masterchekla/ATX-PSU/docs/images/IMG_4238.jpg

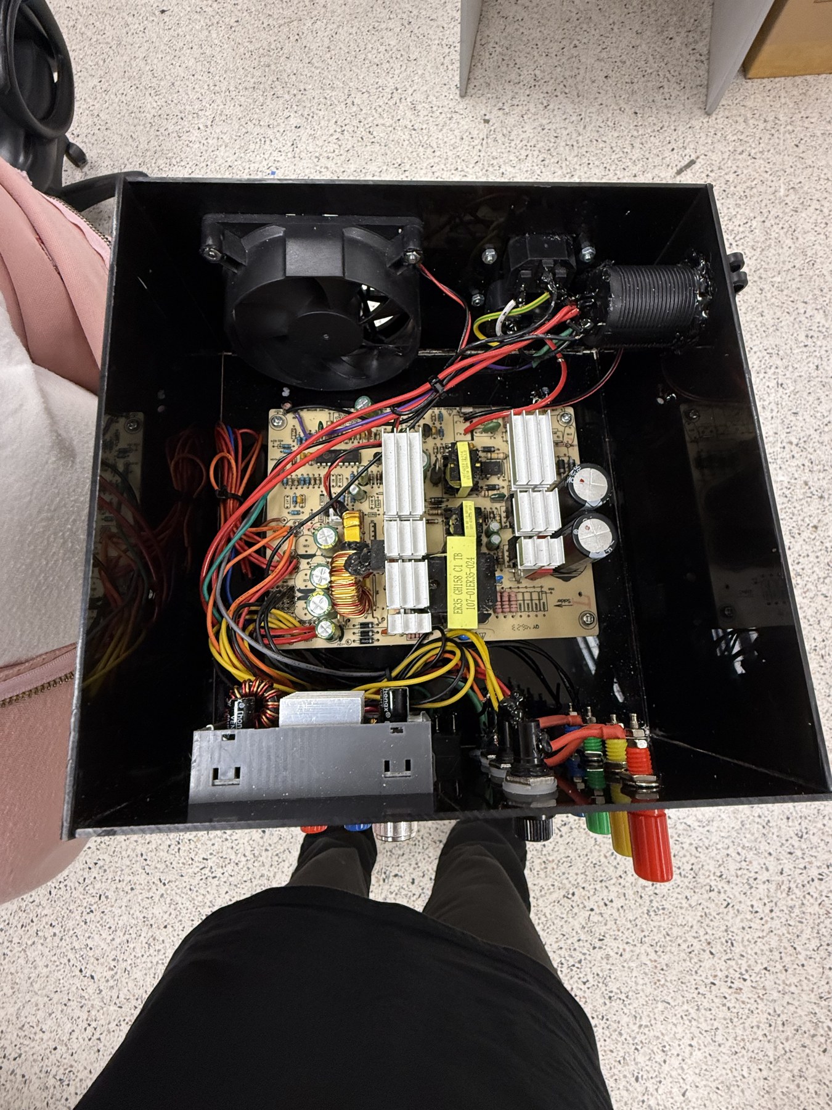
docs/images/IMG_4238.jpg
