masterchekla/ATX-PSU/docs/images/IMG_4239.jpg

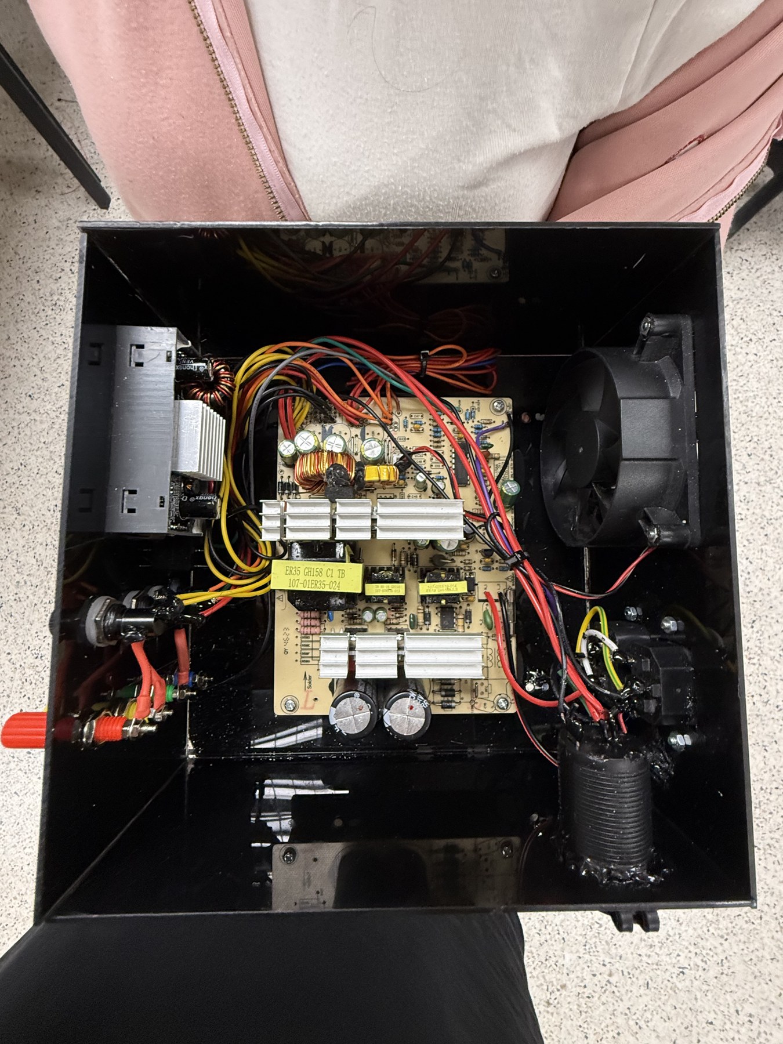
docs/images/IMG_4239.jpg
