masterchekla/ATX-PSU/docs/images/IMG_4240.jpg

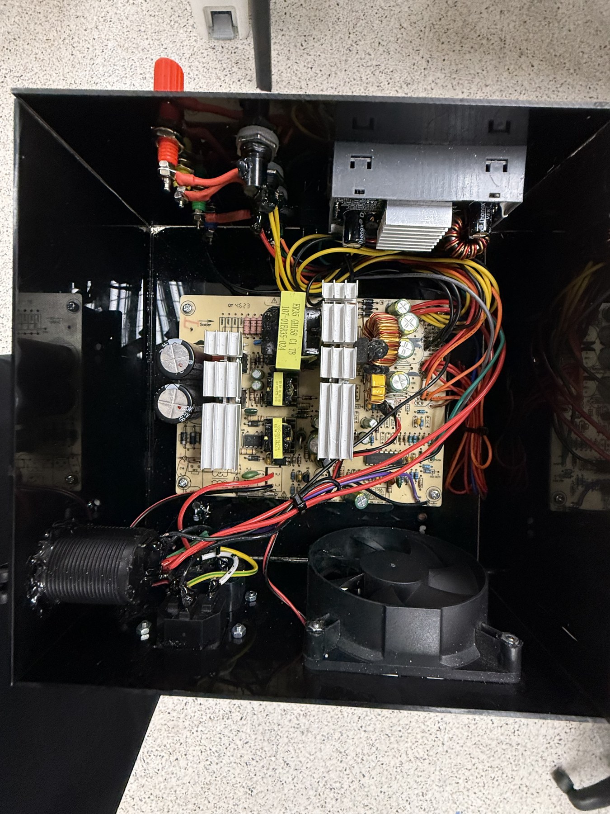
docs/images/IMG_4240.jpg
