masterchekla/ATX-PSU/docs/images/IMG_4241.jpg

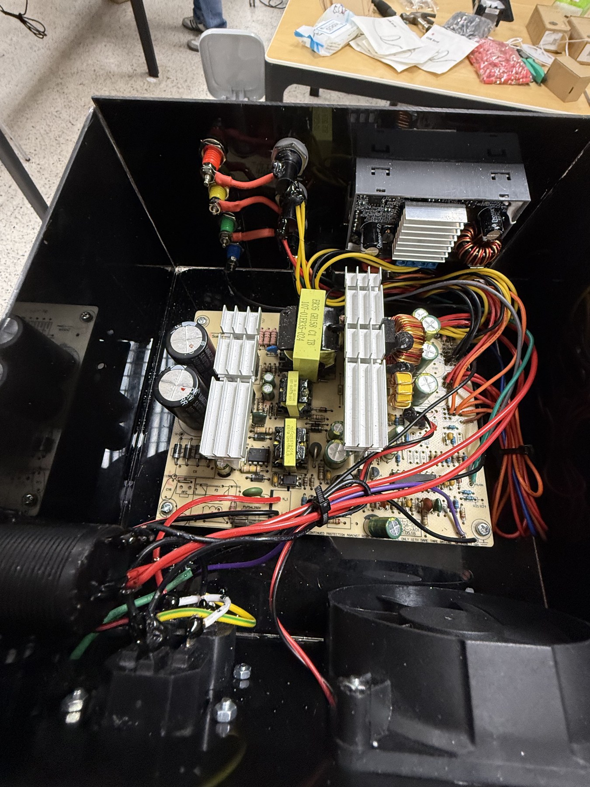
docs/images/IMG_4241.jpg
