masterchekla/ATX-PSU/docs/images/IMG_4242.jpg

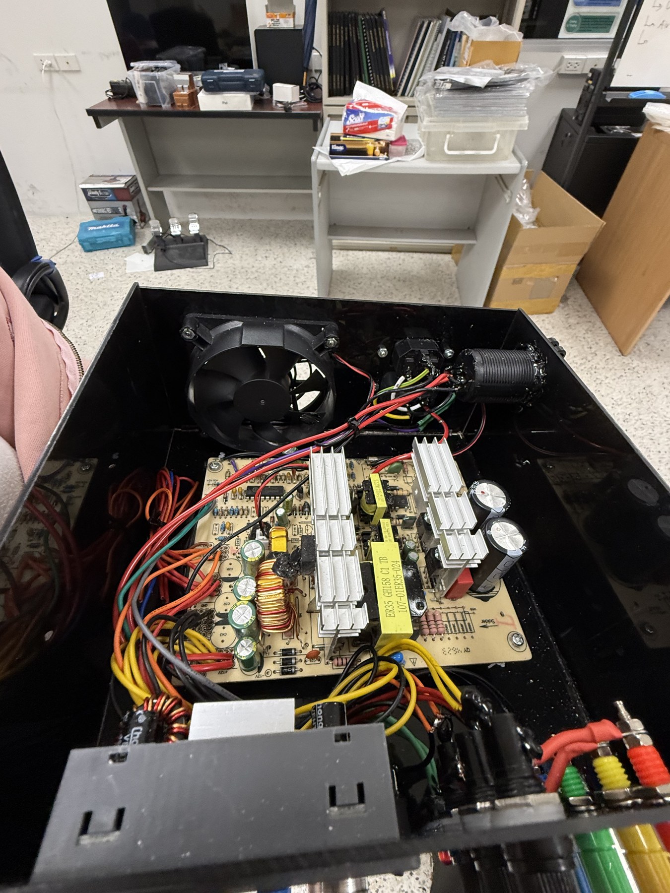
docs/images/IMG_4242.jpg
