masterchekla/ATX-PSU/docs/images/IMG_4243.jpg

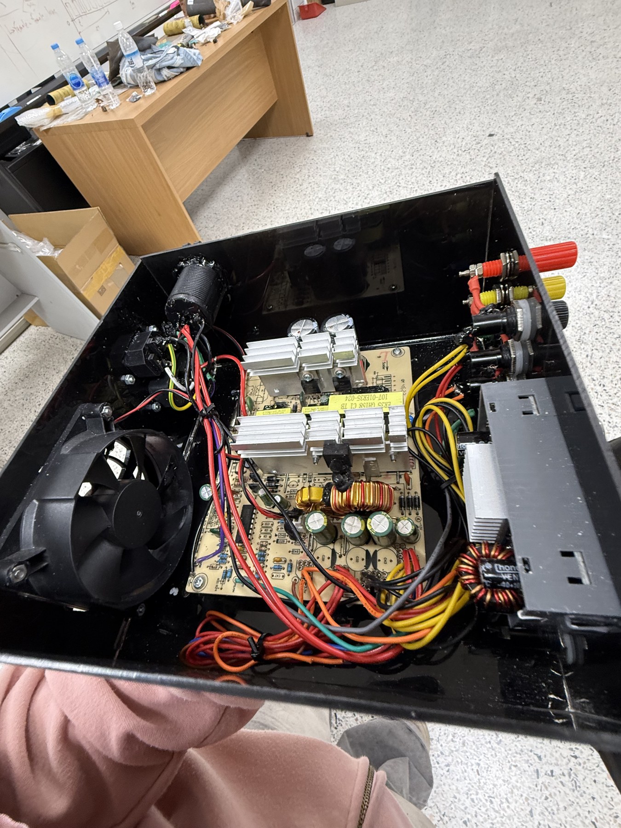
docs/images/IMG_4243.jpg
