masterchekla/ATX-PSU/docs/images/IMG_4244.jpg

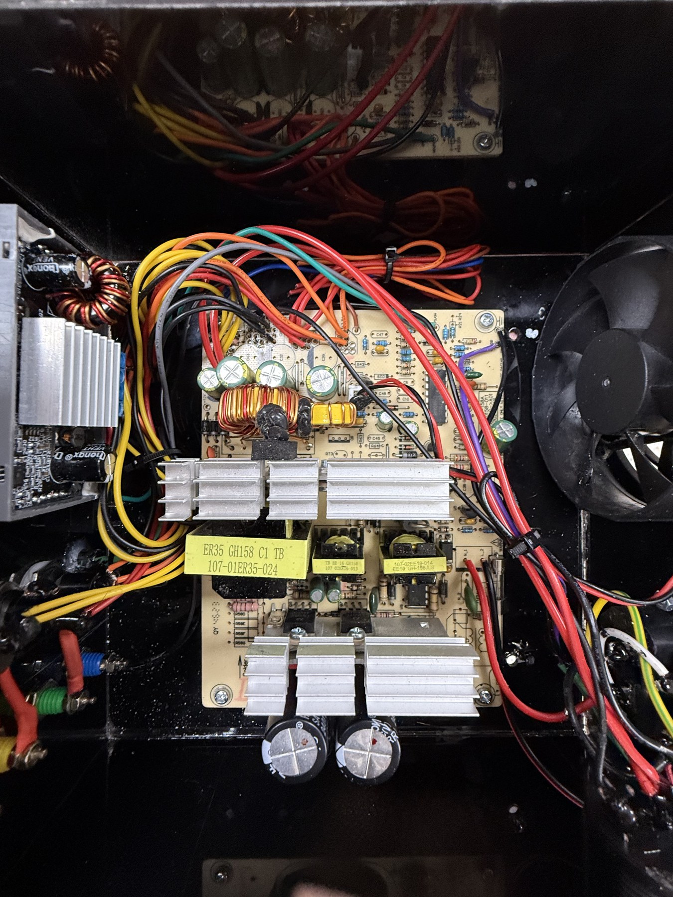
docs/images/IMG_4244.jpg
