masterchekla/ATX-PSU/docs/images/IMG_4245.jpg

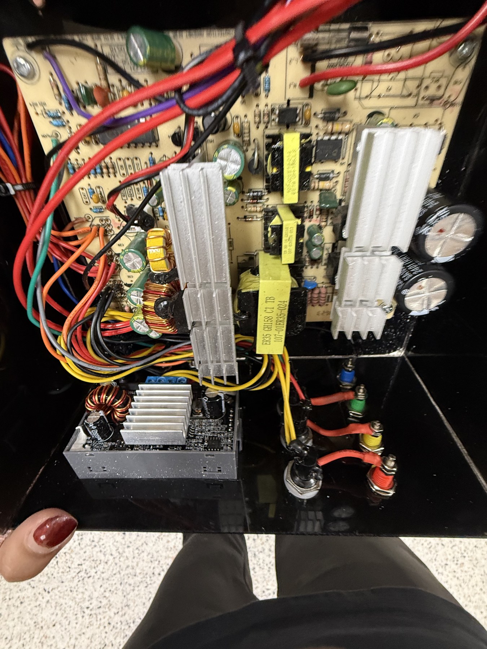
docs/images/IMG_4245.jpg
