masterchekla/ATX-PSU/docs/images/IMG_4246.jpg

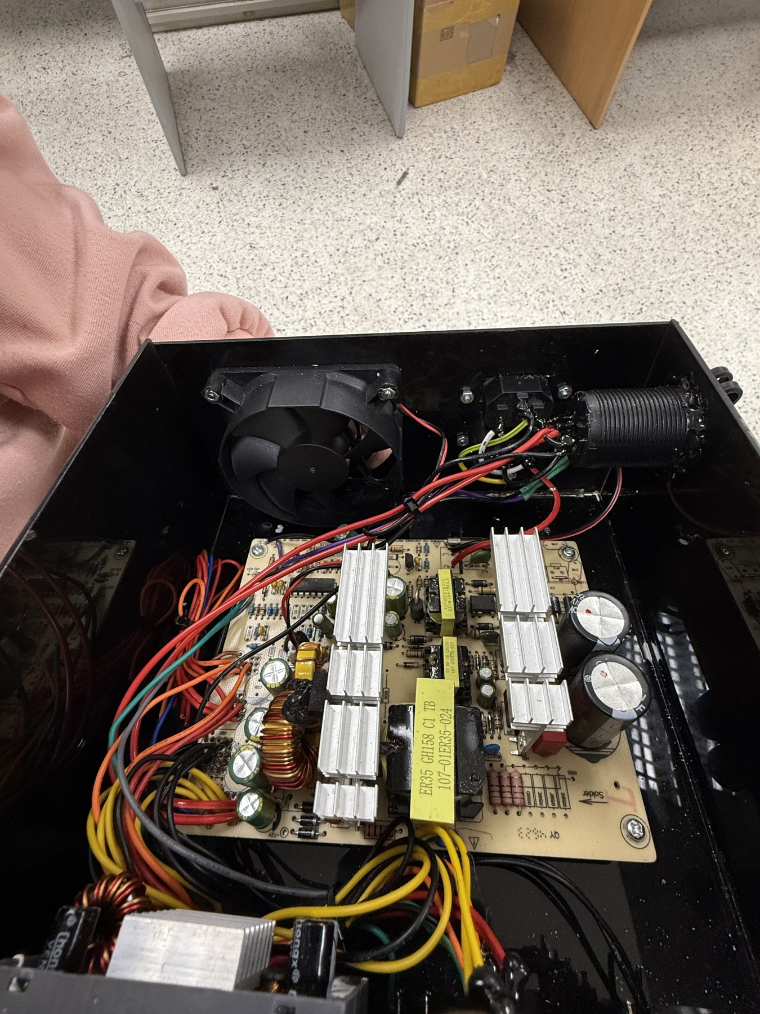
docs/images/IMG_4246.jpg
