masterchekla/ATX-PSU/docs/images/IMG_4295.jpg

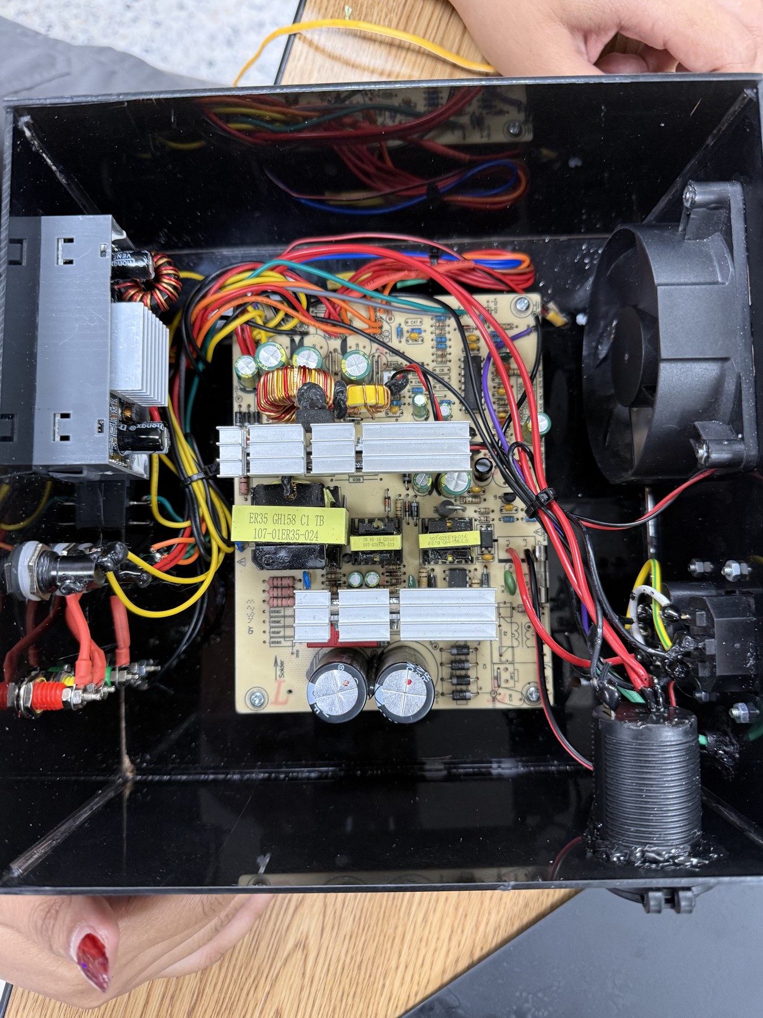
docs/images/IMG_4295.jpg
