masterchekla/ATX-PSU/docs/images/IMG_4296.jpg

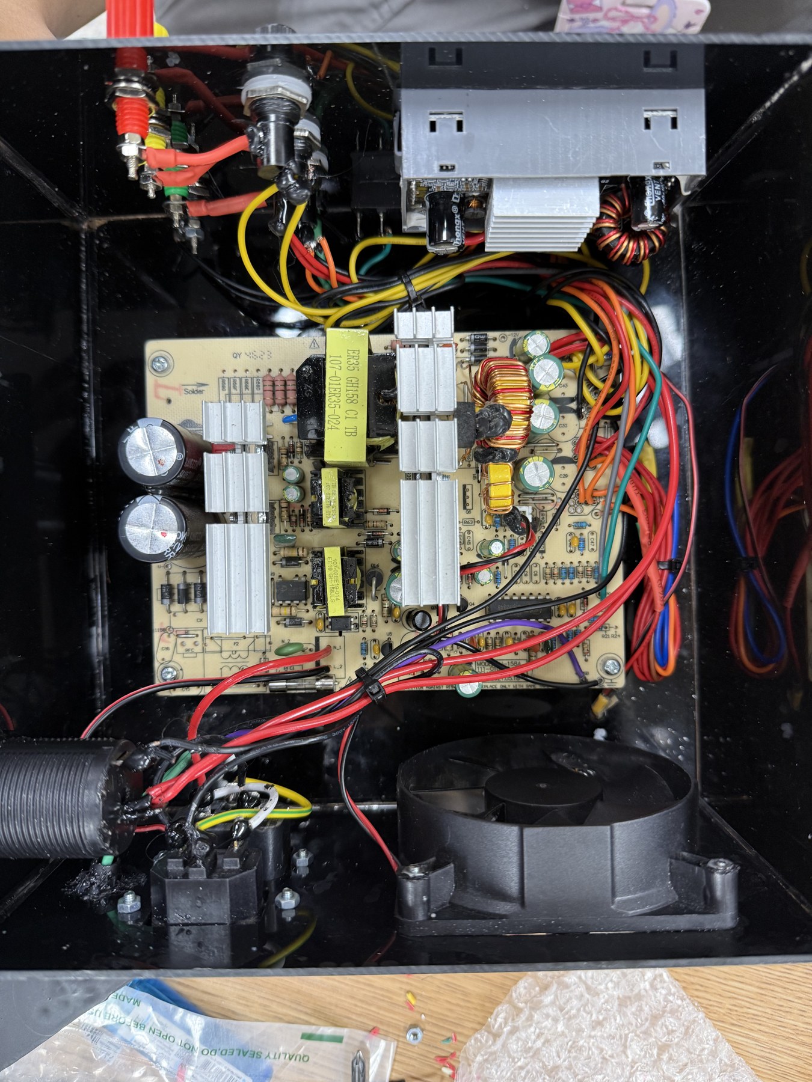
docs/images/IMG_4296.jpg
