masterchekla/ATX-PSU/docs/images/IMG_4297.jpg

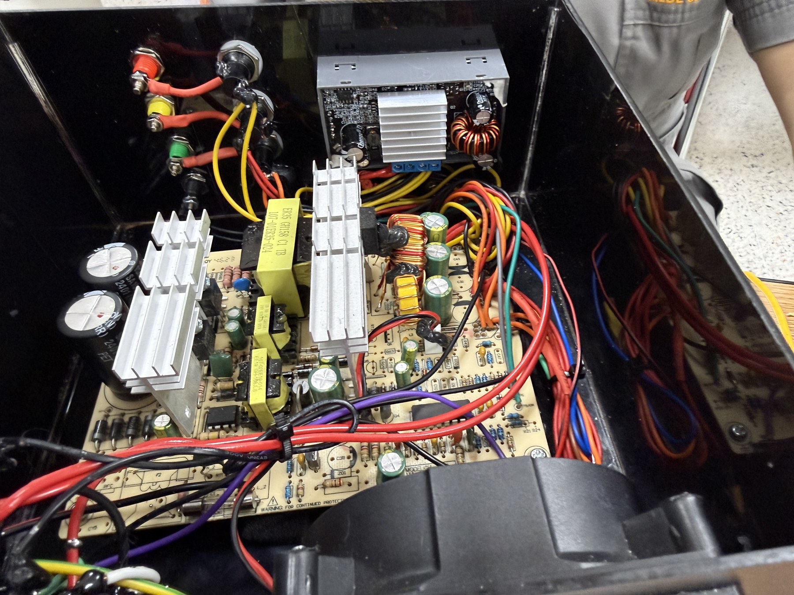
docs/images/IMG_4297.jpg
