masterchekla/ATX-PSU/docs/images/IMG_4298.jpg

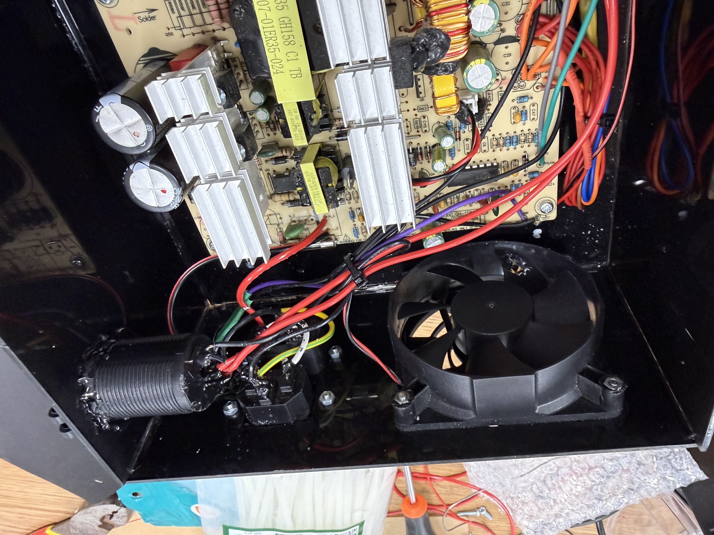
docs/images/IMG_4298.jpg
