masterchekla/ATX-PSU/docs/images/IMG_4303.jpg

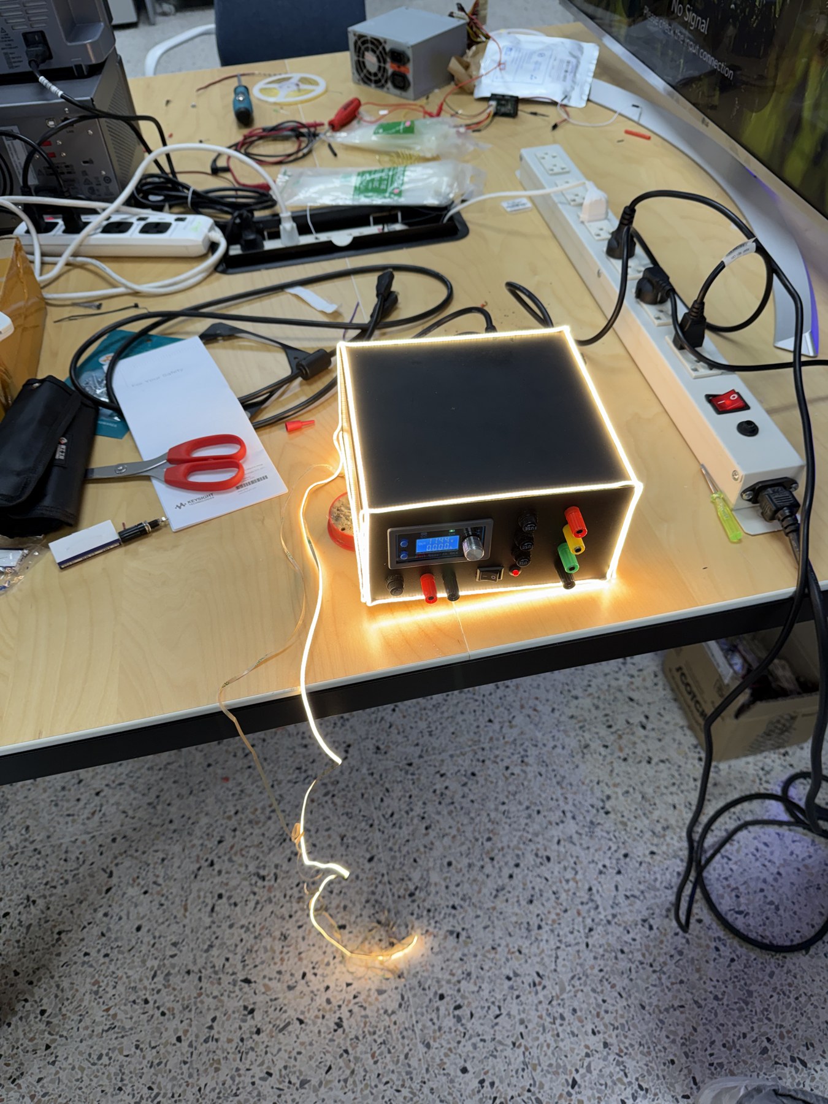
docs/images/IMG_4303.jpg
