masterchekla/ATX-PSU/docs/images/IMG_4305.jpg

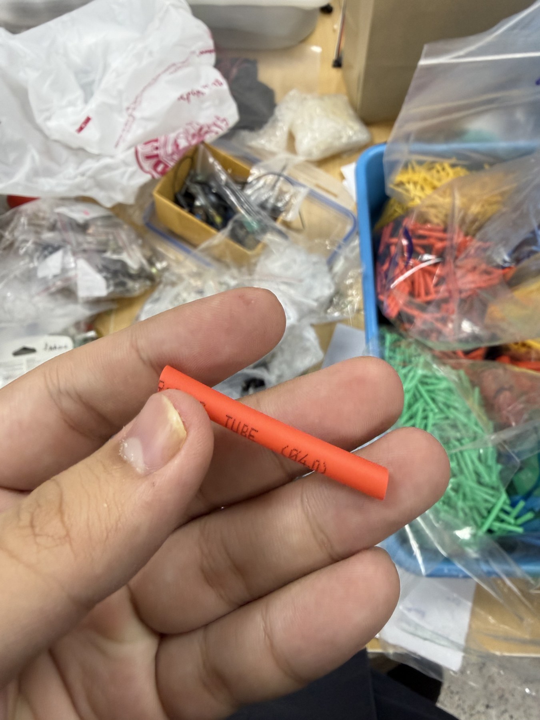
docs/images/IMG_4305.jpg
