masterchekla/ATX-PSU/docs/images/IMG_4306.jpg

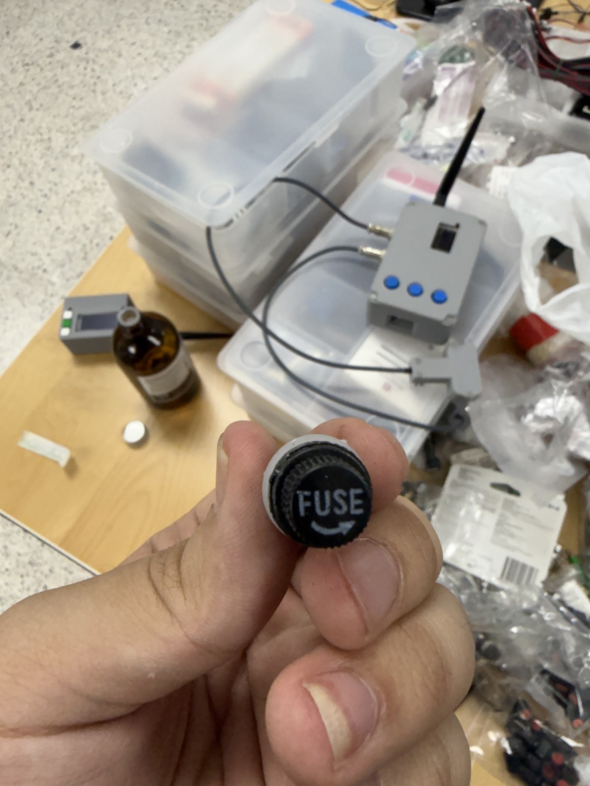
docs/images/IMG_4306.jpg
