masterchekla/ATX-PSU/docs/images/IMG_4307.jpg

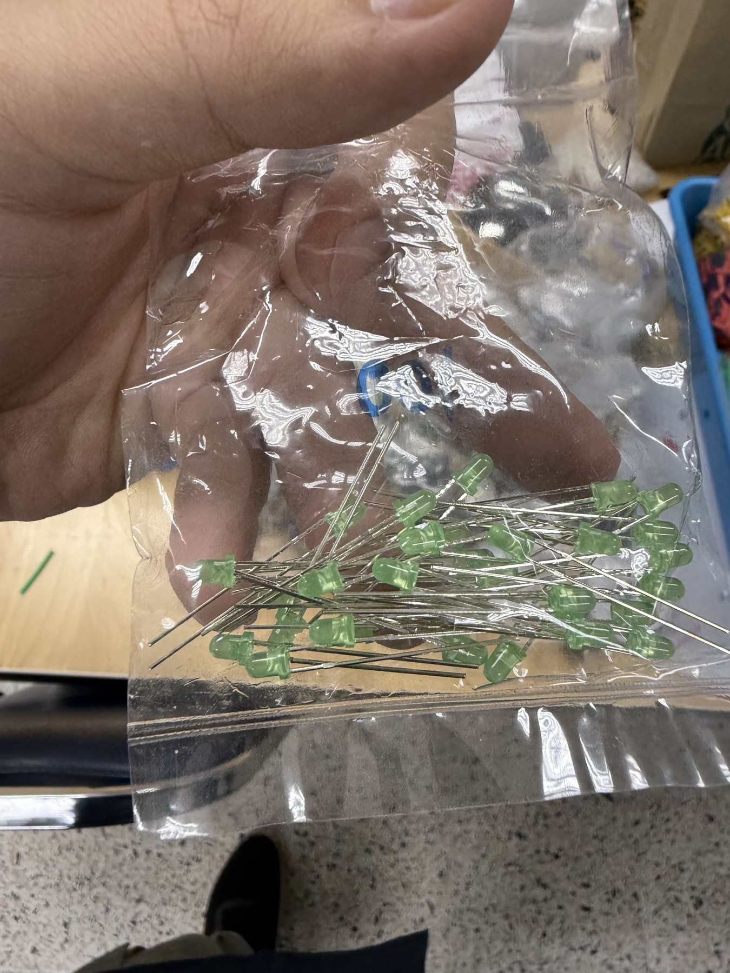
docs/images/IMG_4307.jpg
