masterchekla/ATX-PSU/docs/images/IMG_4308.jpg

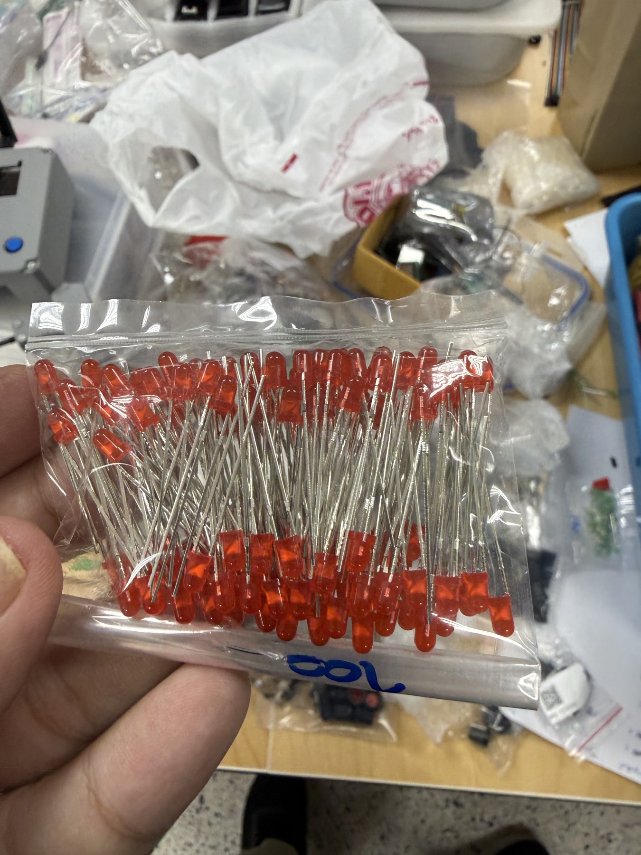
docs/images/IMG_4308.jpg
