masterchekla/ATX-PSU/docs/images/IMG_4309.jpg

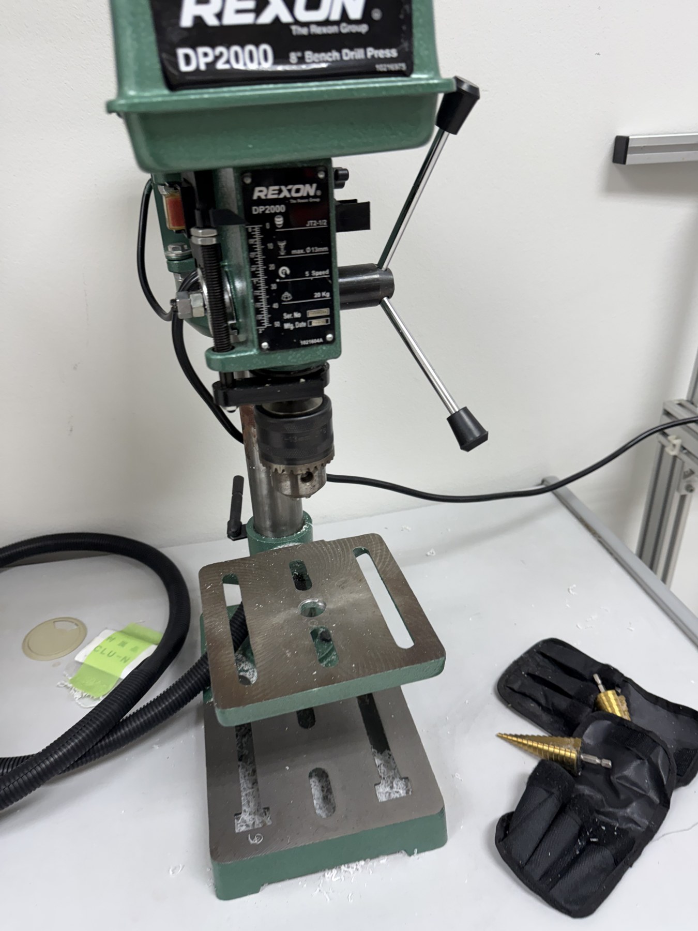
docs/images/IMG_4309.jpg
