masterchekla/ATX-PSU/docs/images/IMG_4310.jpg

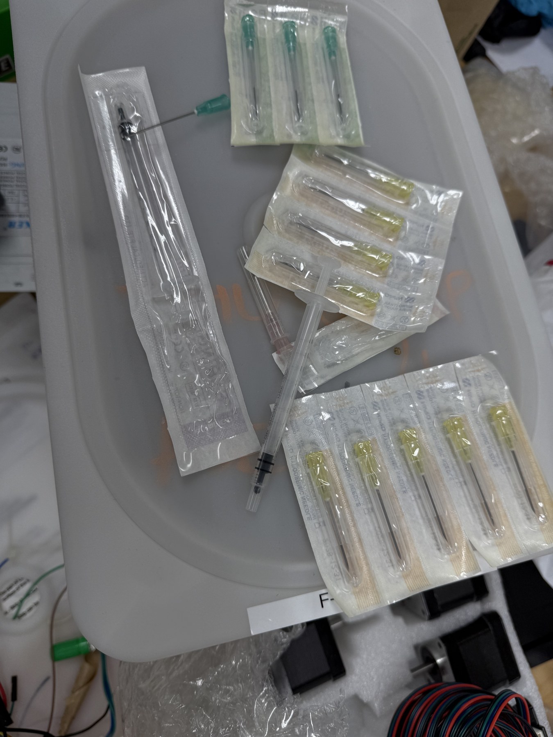
docs/images/IMG_4310.jpg
