masterchekla/ATX-PSU/docs/images/IMG_4311.jpg

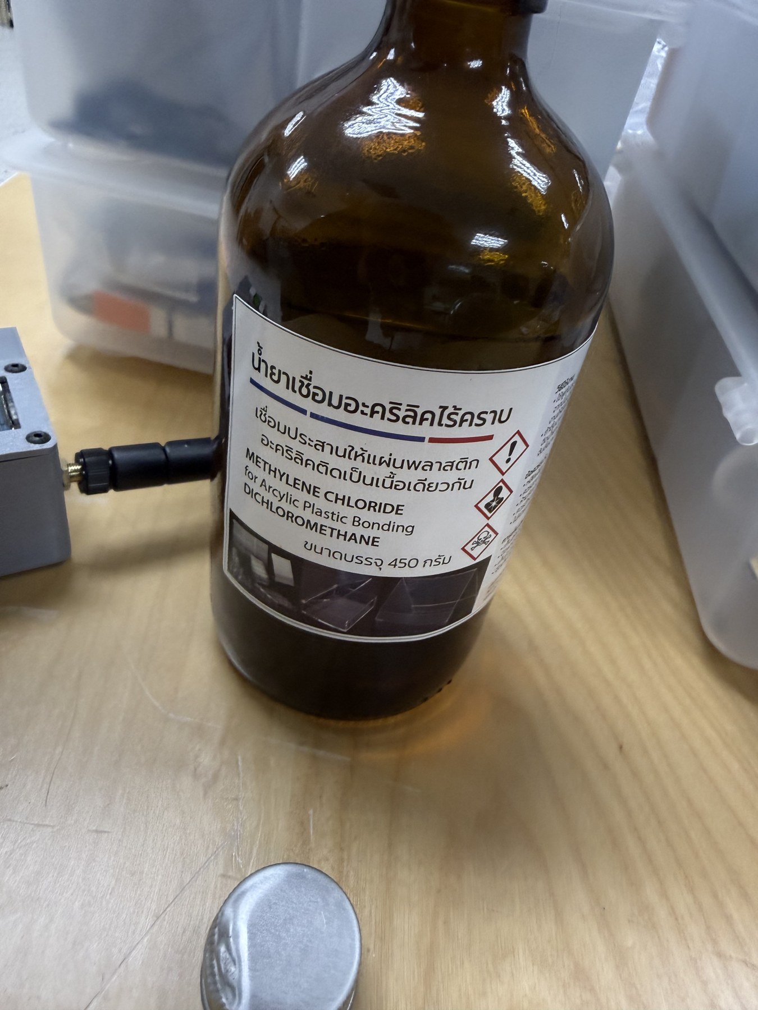
docs/images/IMG_4311.jpg
