masterchekla/ATX-PSU/docs/images/IMG_4312.jpg

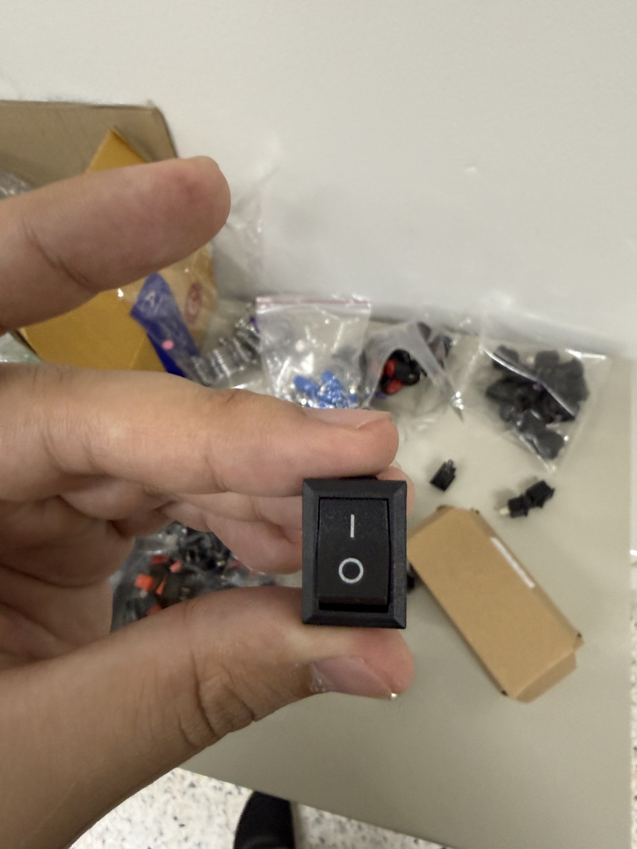
docs/images/IMG_4312.jpg
