masterchekla/ATX-PSU/docs/images/IMG_4313.jpg

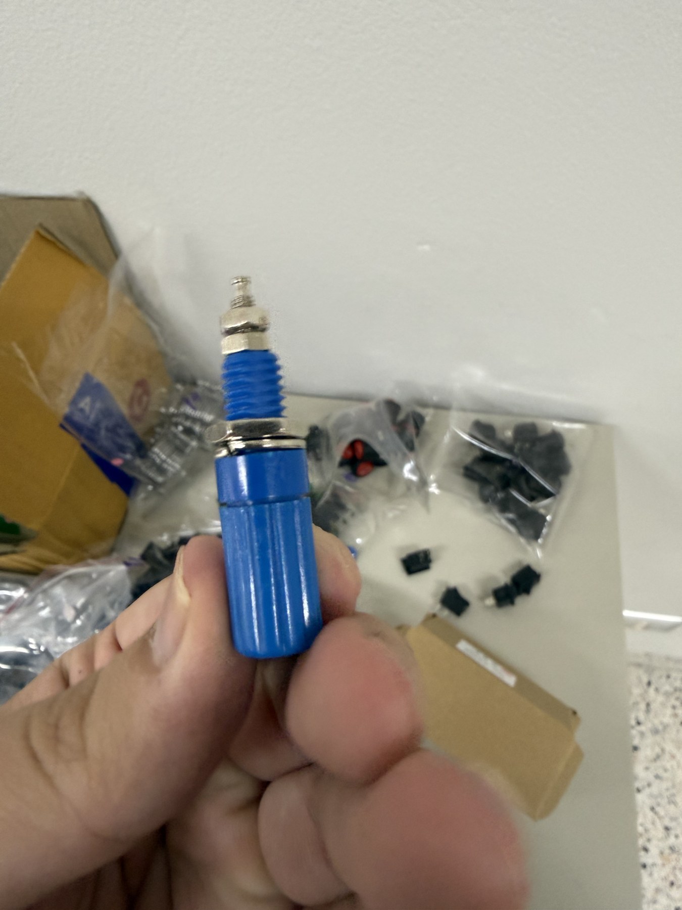
docs/images/IMG_4313.jpg
