masterchekla/ATX-PSU/docs/images/IMG_4314.jpg

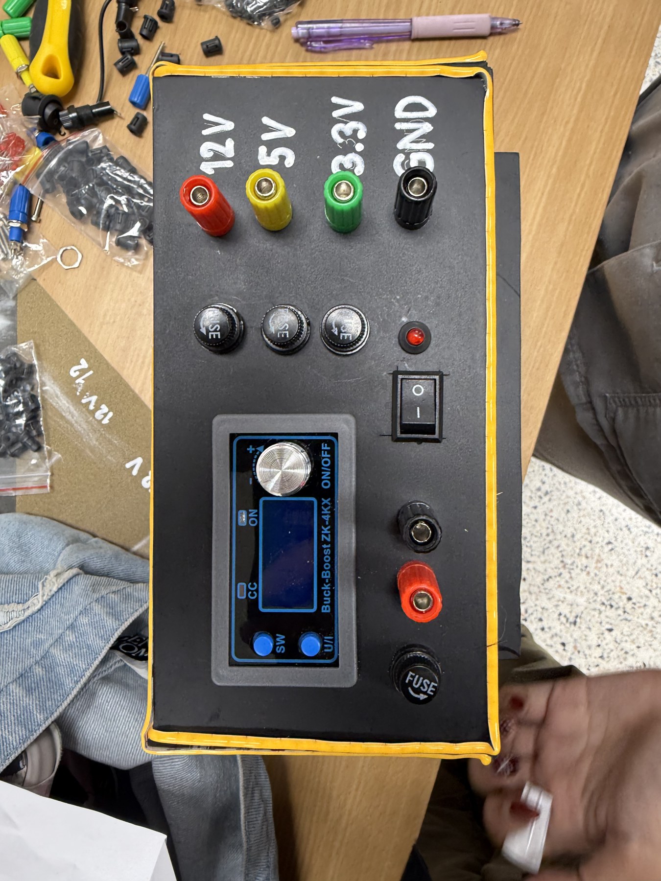
docs/images/IMG_4314.jpg
