masterchekla/ATX-PSU/docs/images/IMG_4315.jpg

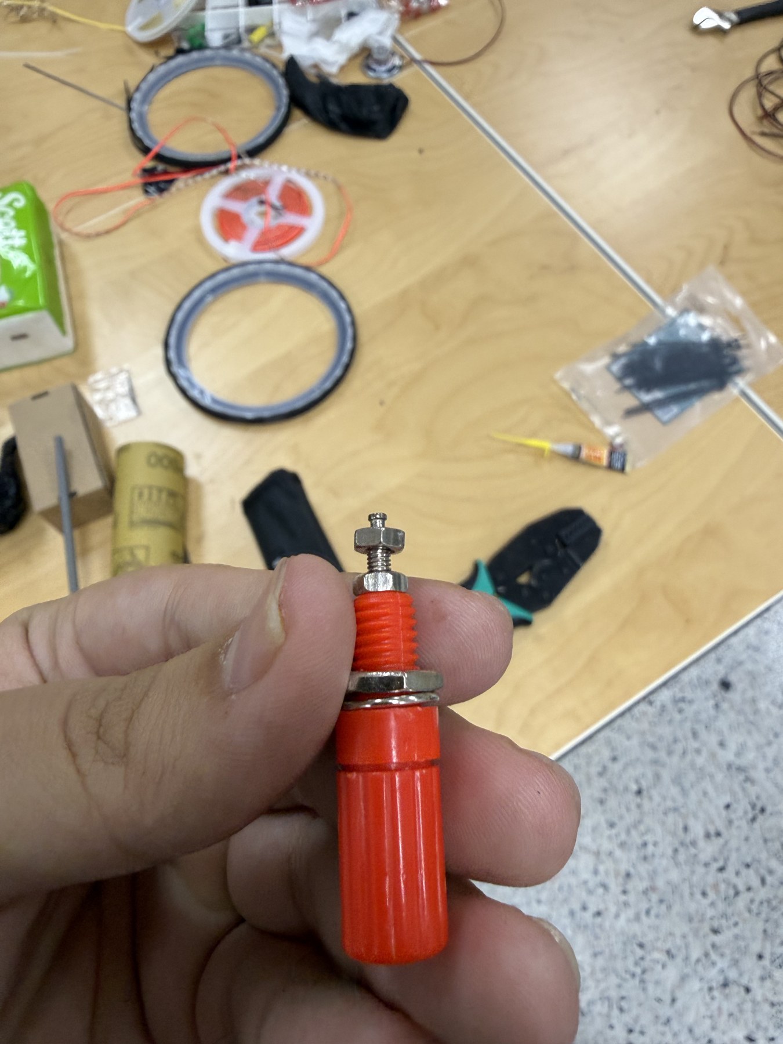
docs/images/IMG_4315.jpg
