masterchekla/ATX-PSU/docs/images/IMG_4316.jpg

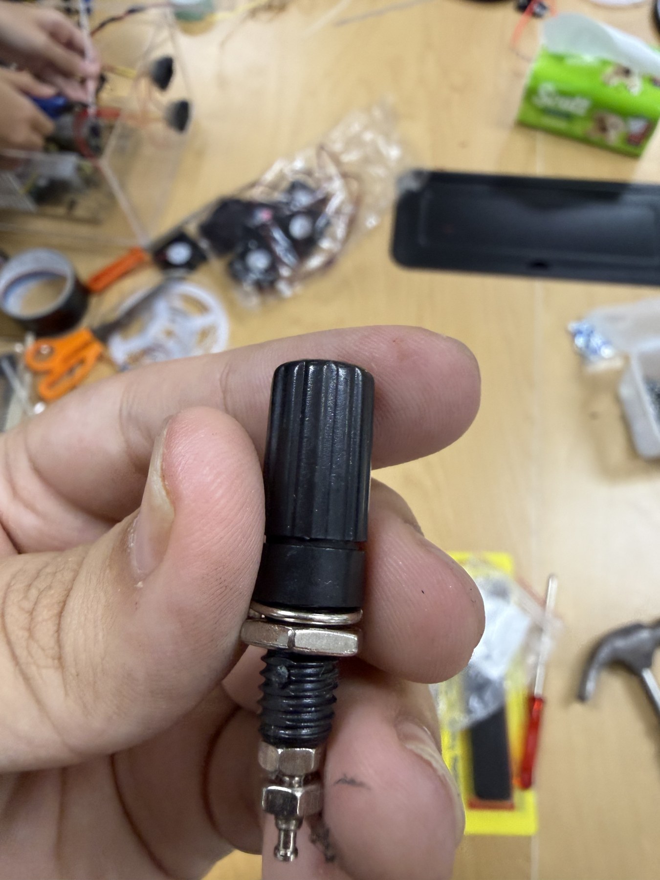
docs/images/IMG_4316.jpg
