masterchekla/ATX-PSU/hardware/diy_atx_psu.kicad_sch

## KiCad design hardware/diy_atx_psu.kicad_sch (2026-10-01)

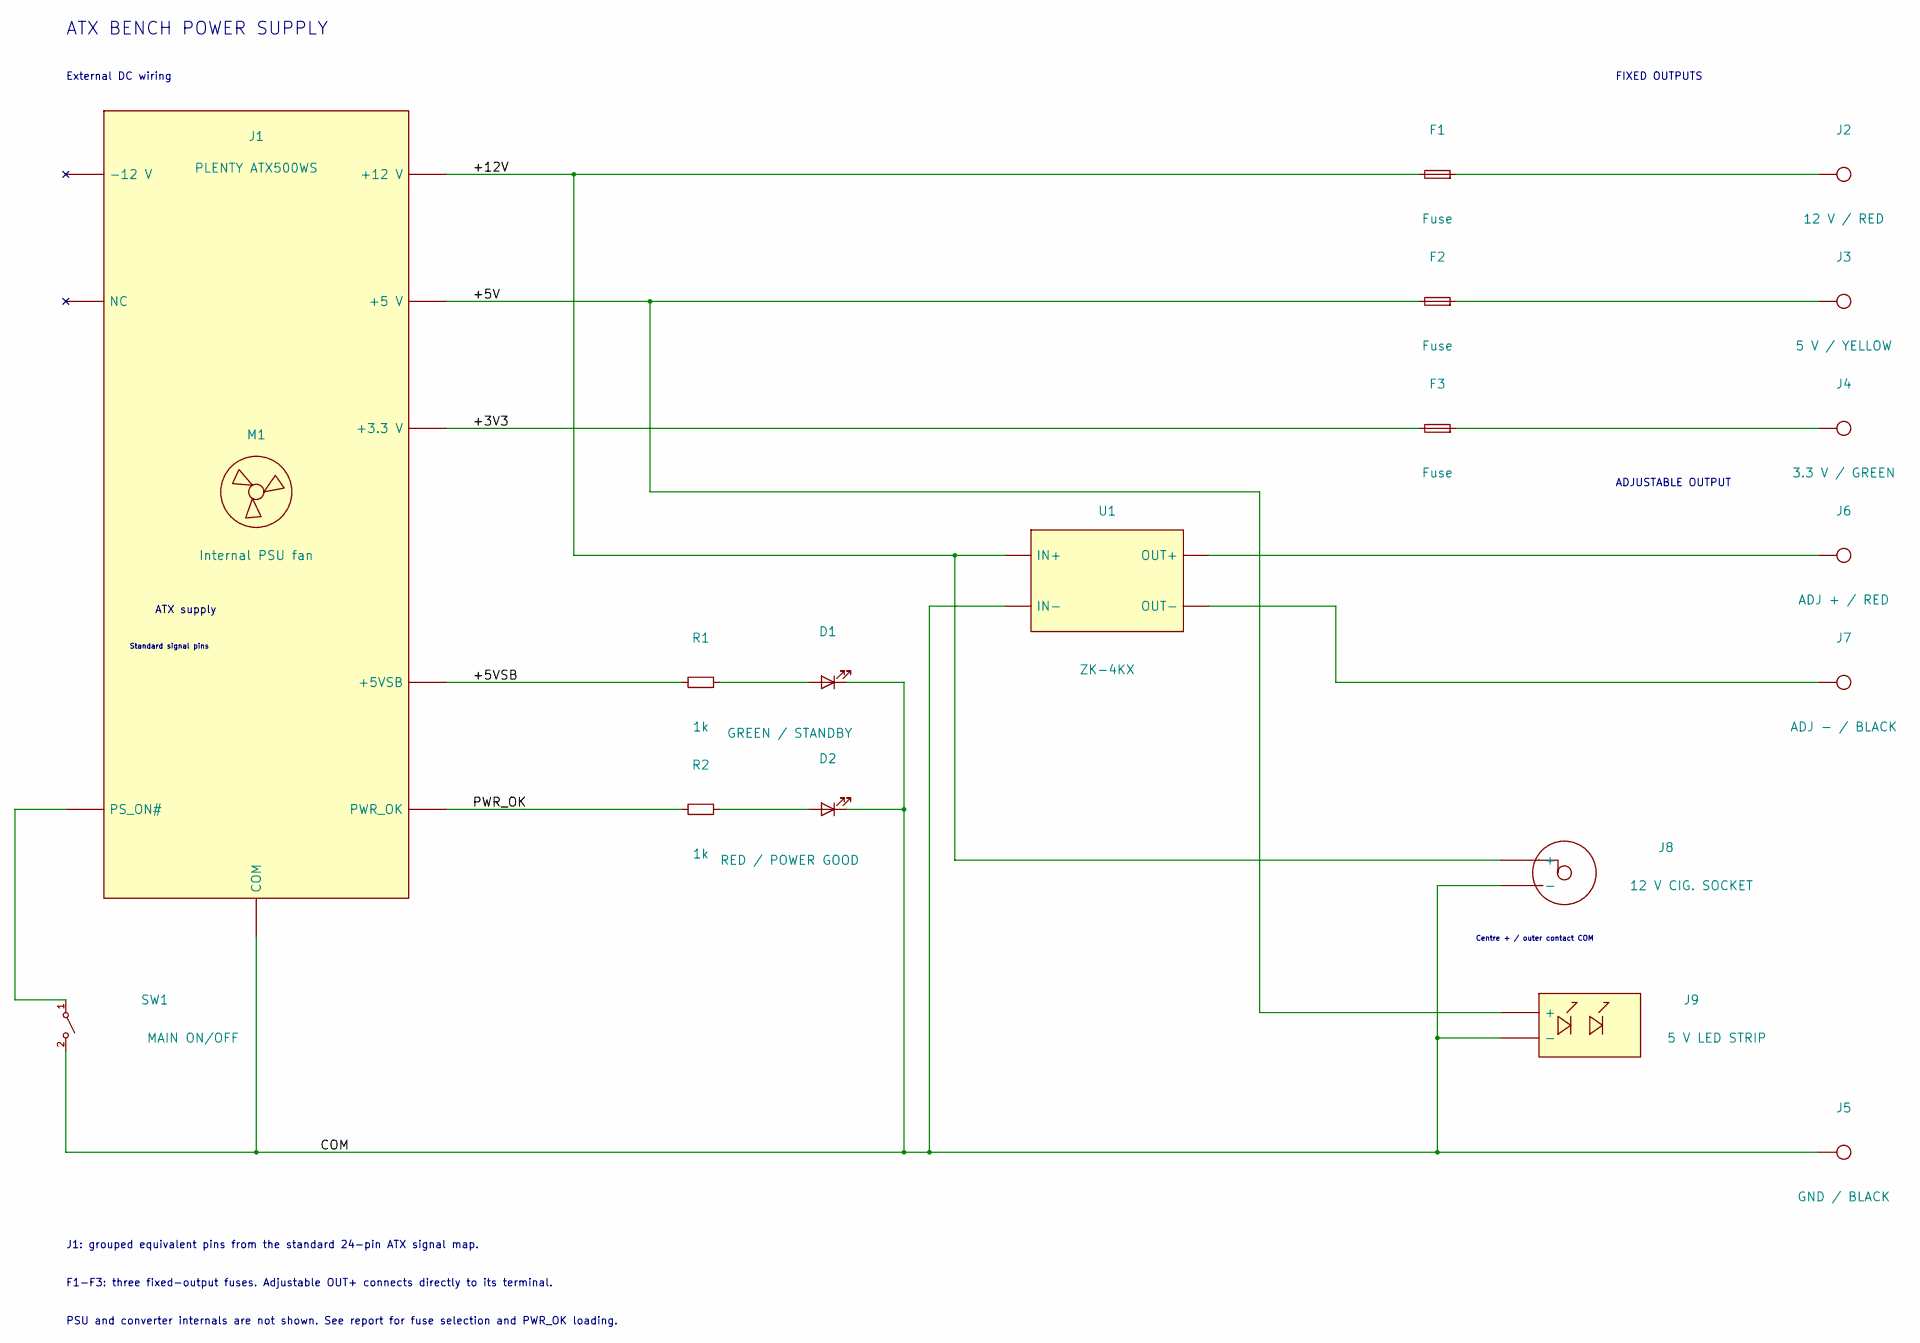
[picture p31: schematic diy_atx_psu.kicad_sch]

Parts:
D1: GREEN / STANDBY
D2: RED / POWER GOOD
F1, F2, F3: Fuse
J1: PLENTY ATX500WS
J2: 12 V / RED
J3: 5 V / YELLOW
J4: 3.3 V / GREEN
J5: GND / BLACK
J6: ADJ + / RED
J7: ADJ - / BLACK
J8: 12 V CIG. SOCKET
J9: 5 V LED STRIP
M1: Internal PSU fan
R1, R2: 1k
SW1: MAIN ON/OFF
U1: ZK-4KX

Connections:
+3V3: F3.1, J1.1 (+3.3 V), J1.2 (+3.3 V), J1.12 (+3.3 V), J1.13 (+3.3 V)
+5V: F2.1, J1.4 (+5 V), J1.6 (+5 V), J1.21 (+5 V), J1.22 (+5 V), J1.23 (+5 V), J9.1 (+)
+5VSB: J1.9 (+5VSB), R1.1
+12V: F1.1, J1.10 (+12 V), J1.11 (+12 V), J8.1 (+), U1.1 (IN+)
COM: D1.1 (K), D2.1 (K), J1.3 (COM), J1.5 (COM), J1.7 (COM), J1.15 (COM), J1.17 (COM), J1.18 (COM), J1.19 (COM), J1.24 (COM), J5.1, J8.2 (-), J9.2 (-), SW1.2 (B), U1.2 (IN-)
unnamed: D1.2 (A), R1.2
unnamed: D2.2 (A), R2.2
unnamed: F1.2, J2.1
unnamed: F2.2, J3.1
unnamed: F3.2, J4.1
unnamed: J1.16 (PS_ON#), SW1.1 (A)
unnamed: J6.1, U1.3 (OUT+)
unnamed: J7.1, U1.4 (OUT-)
PWR_OK: J1.8 (PWR_OK), R2.1

Notes on the sheet:
ATX BENCH POWER SUPPLY
External DC wiring
ATX supply
Standard signal pins
FIXED OUTPUTS
ADJUSTABLE OUTPUT
Centre + / outer contact COM
J1: grouped equivalent pins from the standard 24-pin ATX signal map.
F1-F3: three fixed-output fuses. Adjustable OUT+ connects directly to its terminal.
PSU and converter internals are not shown. See report for fuse selection and PWR_OK loading.
